Mikroudz/sulautetut-jarjestelmat/STM32F410/Src/vl53l1_platform.c

/* 
* This file is part of VL53L1 Platform 
* 
* Copyright (c) 2016, STMicroelectronics - All Rights Reserved 
* 
* License terms: BSD 3-clause "New" or "Revised" License. 
* 
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
* 3. Neither the name of the copyright holder nor the names of its contributors 
* may be used to endorse or promote products derived from this software 
* without specific prior written permission. 
* 
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
*/

#include "vl53l1_platform.h"
#include <string.h>
#include <time.h>
#include <math.h>
#include "vl53l1_error_codes.h"

#include "i2c.h"

#define I2C_TIME_OUT_BASE   10
#define I2C_TIME_OUT_BYTE   1

/* when not customized by application define dummy one */
#ifndef VL53L1_GetI2cBus
/** This macro can be overloaded by user to enforce i2c sharing in RTOS context
 */
#   define VL53L1_GetI2cBus(...) (void)0
#endif

#ifndef VL53L1_PutI2cBus
/** This macro can be overloaded by user to enforce i2c sharing in RTOS context
 */
#   define VL53L1_PutI2cBus(...) (void)0
#endif
I2C_HandleTypeDef hi2c2;


uint8_t _I2CBuffer[256];

int _I2CWrite(uint16_t Dev, uint8_t *pdata, uint32_t count) {
    int status;
    int i2c_time_out = I2C_TIME_OUT_BASE + count * I2C_TIME_OUT_BYTE;

    status = HAL_I2C_Master_Transmit(&hi2c2, Dev, pdata, count, i2c_time_out);
    if (status) {
        //VL6180x_ErrLog("I2C error 0x%x %d len", dev->I2cAddr, len);
        //XNUCLEO6180XA1_I2C1_Init(&hi2c2);
    }
    return status;
}

// Alustava DMA-funktio, ei vielä käytössä
int _I2CWrite_DMA(uint16_t Dev, uint8_t *pdata, uint32_t count) {
    int status;

    status = HAL_I2C_Master_Transmit_DMA(&hi2c2, Dev, pdata, count);
    if (status) {
        //VL6180x_ErrLog("I2C error 0x%x %d len", dev->I2cAddr, len);
        //XNUCLEO6180XA1_I2C1_Init(&hi2c2);
    }
    return status;
}

int _I2CRead(uint16_t Dev, uint8_t *pdata, uint32_t count) {
    int status;
    int i2c_time_out = I2C_TIME_OUT_BASE+ count* I2C_TIME_OUT_BYTE;

    status = HAL_I2C_Master_Receive(&hi2c2, Dev | 1, pdata, count, i2c_time_out);
    if (status) {
        //VL6180x_ErrLog("I2C error 0x%x %d len", dev->I2cAddr, len);
        //XNUCLEO6180XA1_I2C1_Init(&hi2c2);
    }
    return status;
}

// Alustava DMA-funktio, ei vielä käytössä
int _I2CRead_DMA(uint16_t Dev, uint8_t *pdata, uint32_t count){
    int status;

    status = HAL_I2C_Master_Receive_DMA(&hi2c2, Dev | 1, pdata, count);
    if (status) {
        //VL6180x_ErrLog("I2C error 0x%x %d len", dev->I2cAddr, len);
        //XNUCLEO6180XA1_I2C1_Init(&hi2c2);
    }
    return status;
}

int8_t VL53L1_WriteMulti( uint16_t Dev, uint16_t index, uint8_t *pdata, uint32_t count) {
	int status_int;
    VL53L1_Error Status = VL53L1_ERROR_NONE;
    if (count > sizeof(_I2CBuffer) - 1) {
        return VL53L1_ERROR_INVALID_PARAMS;
    }
    _I2CBuffer[0] = index>>8;
    _I2CBuffer[1] = index&0xFF;
    memcpy(&_I2CBuffer[2], pdata, count);
    VL53L1_GetI2cBus();
    status_int = _I2CWrite(Dev, _I2CBuffer, count + 2);
    if (status_int != 0) {
        Status = VL53L1_ERROR_CONTROL_INTERFACE;
    }
    VL53L1_PutI2cBus();
    return Status;
}

VL53L1_Error VL53L1_ReadMulti(uint16_t Dev, uint16_t index, uint8_t *pdata, uint32_t count) {
    VL53L1_Error Status = VL53L1_ERROR_NONE;
    int32_t status_int;

    _I2CBuffer[0] = index>>8;
    _I2CBuffer[1] = index&0xFF;
    VL53L1_GetI2cBus();
    status_int = _I2CWrite(Dev, _I2CBuffer, 2);
    if (status_int != 0) {
        Status = VL53L1_ERROR_CONTROL_INTERFACE;
        goto done;
    }
    status_int = _I2CRead(Dev, pdata, count);
    if (status_int != 0) {
        Status = VL53L1_ERROR_CONTROL_INTERFACE;
    }
done:
    VL53L1_PutI2cBus();
    return Status;
}

VL53L1_Error VL53L1_WrByte(uint16_t Dev, uint16_t index, uint8_t data) {
    VL53L1_Error Status = VL53L1_ERROR_NONE;
    int32_t status_int;

    _I2CBuffer[0] = index>>8;
    _I2CBuffer[1] = index&0xFF;
    _I2CBuffer[2] = data;

    VL53L1_GetI2cBus();
    status_int = _I2CWrite(Dev, _I2CBuffer, 3);
    if (status_int != 0) {
        Status = VL53L1_ERROR_CONTROL_INTERFACE;
    }
    VL53L1_PutI2cBus();
    return Status;
}

VL53L1_Error VL53L1_WrWord(uint16_t Dev, uint16_t index, uint16_t data) {
    VL53L1_Error Status = VL53L1_ERROR_NONE;
    int32_t status_int;

    _I2CBuffer[0] = index>>8;
    _I2CBuffer[1] = index&0xFF;
    _I2CBuffer[2] = data >> 8;
    _I2CBuffer[3] = data & 0x00FF;

    VL53L1_GetI2cBus();
    status_int = _I2CWrite(Dev, _I2CBuffer, 4);
    if (status_int != 0) {
        Status = VL53L1_ERROR_CONTROL_INTERFACE;
    }
    VL53L1_PutI2cBus();
    return Status;
}

VL53L1_Error VL53L1_WrDWord(uint16_t Dev, uint16_t index, uint32_t data) {
    VL53L1_Error Status = VL53L1_ERROR_NONE;
    int32_t status_int;
    _I2CBuffer[0] = index>>8;
    _I2CBuffer[1] = index&0xFF;
    _I2CBuffer[2] = (data >> 24) & 0xFF;
    _I2CBuffer[3] = (data >> 16) & 0xFF;
    _I2CBuffer[4] = (data >> 8)  & 0xFF;
    _I2CBuffer[5] = (data >> 0 ) & 0xFF;
    VL53L1_GetI2cBus();
    status_int = _I2CWrite(Dev, _I2CBuffer, 6);
    if (status_int != 0) {
        Status = VL53L1_ERROR_CONTROL_INTERFACE;
    }
    VL53L1_PutI2cBus();
    return Status;
}

VL53L1_Error VL53L1_UpdateByte(uint16_t Dev, uint16_t index, uint8_t AndData, uint8_t OrData) {
    VL53L1_Error Status = VL53L1_ERROR_NONE;
    uint8_t data;

    Status = VL53L1_RdByte(Dev, index, &data);
    if (Status) {
        goto done;
    }
    data = (data & AndData) | OrData;
    Status = VL53L1_WrByte(Dev, index, data);
done:
    return Status;
}

VL53L1_Error VL53L1_RdByte(uint16_t Dev, uint16_t index, uint8_t *data) {
    VL53L1_Error Status = VL53L1_ERROR_NONE;
    int32_t status_int;

	_I2CBuffer[0] = index>>8;
	_I2CBuffer[1] = index&0xFF;
    VL53L1_GetI2cBus();
    status_int = _I2CWrite(Dev, _I2CBuffer, 2);
    if( status_int ){
        Status = VL53L1_ERROR_CONTROL_INTERFACE;
        goto done;
    }
    status_int = _I2CRead(Dev, data, 1);
    if (status_int != 0) {
        Status = VL53L1_ERROR_CONTROL_INTERFACE;
    }
done:
    VL53L1_PutI2cBus();
    return status_int;
}

VL53L1_Error VL53L1_RdWord(uint16_t Dev, uint16_t index, uint16_t *data) {
    VL53L1_Error Status = VL53L1_ERROR_NONE;
    int32_t status_int;

    _I2CBuffer[0] = index>>8;
	_I2CBuffer[1] = index&0xFF;
    VL53L1_GetI2cBus();
    status_int = _I2CWrite(Dev, _I2CBuffer, 2);

    if( status_int ){
        Status = VL53L1_ERROR_CONTROL_INTERFACE;
        goto done;
    }
    status_int = _I2CRead(Dev, _I2CBuffer, 2);
    if (status_int != 0) {
        Status = VL53L1_ERROR_CONTROL_INTERFACE;
        goto done;
    }

    *data = ((uint16_t)_I2CBuffer[0]<<8) + (uint16_t)_I2CBuffer[1];
done:
    VL53L1_PutI2cBus();
    return Status;
}

VL53L1_Error VL53L1_RdWord_DMA(uint16_t Dev, uint16_t index, uint16_t *data) {
    VL53L1_Error Status = VL53L1_ERROR_NONE;
    int32_t status_int;

    _I2CBuffer[0] = index>>8;
	_I2CBuffer[1] = index&0xFF;
    VL53L1_GetI2cBus();
    status_int = _I2CWrite_DMA(Dev, _I2CBuffer, 2);

    if( status_int ){
        Status = VL53L1_ERROR_CONTROL_INTERFACE;
        goto done;
    }
    status_int = _I2CRead_DMA(Dev, _I2CBuffer, 2);
    if (status_int != 0) {
        Status = VL53L1_ERROR_CONTROL_INTERFACE;
        goto done;
    }

    *data = ((uint16_t)_I2CBuffer[0]<<8) + (uint16_t)_I2CBuffer[1];
done:
    VL53L1_PutI2cBus();
    return Status;
}

VL53L1_Error VL53L1_RdDWord(uint16_t Dev, uint16_t index, uint32_t *data) {
    VL53L1_Error Status = VL53L1_ERROR_NONE;
    int32_t status_int;

    _I2CBuffer[0] = index>>8;
	_I2CBuffer[1] = index&0xFF;
    VL53L1_GetI2cBus();
    status_int = _I2CWrite(Dev, _I2CBuffer, 2);
    if (status_int != 0) {
        Status = VL53L1_ERROR_CONTROL_INTERFACE;
        goto done;
    }
    status_int = _I2CRead(Dev, _I2CBuffer, 4);
    if (status_int != 0) {
        Status = VL53L1_ERROR_CONTROL_INTERFACE;
        goto done;
    }

    *data = ((uint32_t)_I2CBuffer[0]<<24) + ((uint32_t)_I2CBuffer[1]<<16) + ((uint32_t)_I2CBuffer[2]<<8) + (uint32_t)_I2CBuffer[3];

done:
    VL53L1_PutI2cBus();
    return Status;
}

VL53L1_Error VL53L1_WaitMs(uint16_t dev, int32_t wait_ms){
	(void)dev;
	HAL_Delay(wait_ms);
    return VL53L1_ERROR_NONE;
}

VL53L1_Error VL53L1_WaitUs(uint16_t dev, int32_t wait_us){
	(void)dev;
	HAL_Delay(wait_us/1000);
    return VL53L1_ERROR_NONE;
}

VL53L1_Error VL53L1_GetTickCount(
	uint32_t *ptick_count_ms)
{

    /* Returns current tick count in [ms] */

	VL53L1_Error status  = VL53L1_ERROR_NONE;

	//*ptick_count_ms = timeGetTime();
	*ptick_count_ms = 0;

#ifdef VL53L1_LOG_ENABLE
	trace_print(
		VL53L1_TRACE_LEVEL_DEBUG,
		"VL53L1_GetTickCount() = %5u ms;\n",
	*ptick_count_ms);
#endif

	return status;
}

VL53L1_Error VL53L1_WaitValueMaskEx(
	uint16_t 			dev,
	uint32_t      timeout_ms,
	uint16_t      index,
	uint8_t       value,
	uint8_t       mask,
	uint32_t      poll_delay_ms)
{

	/*
	 * Platform implementation of WaitValueMaskEx V2WReg script command
	 *
	 * WaitValueMaskEx(
	 *          duration_ms,
	 *          index,
	 *          value,
	 *          mask,
	 *          poll_delay_ms);
	 */

	VL53L1_Error status         = VL53L1_ERROR_NONE;
	uint32_t     start_time_ms = 0;
	uint32_t     current_time_ms = 0;
	uint32_t     polling_time_ms = 0;
	uint8_t      byte_value      = 0;
	uint8_t      found           = 0;
#ifdef VL53L1_LOG_ENABLE
	uint8_t      trace_functions = VL53L1_TRACE_FUNCTION_NONE;
#endif

//	char   register_name[VL53L1_MAX_STRING_LENGTH];

    /* look up register name */
#ifdef PAL_EXTENDED
	VL53L1_get_register_name(
			index,
			register_name);
#else
//	VL53L1_COPYSTRING(register_name, "");
#endif

	/* Output to I2C logger for FMT/DFT  */

    /*trace_i2c("WaitValueMaskEx(%5d, 0x%04X, 0x%02X, 0x%02X, %5d);\n",
    		     timeout_ms, index, value, mask, poll_delay_ms); */
   // trace_i2c("WaitValueMaskEx(%5d, %s, 0x%02X, 0x%02X, %5d);\n",
    //		     timeout_ms, register_name, value, mask, poll_delay_ms);

	/* calculate time limit in absolute time */

	 VL53L1_GetTickCount(&start_time_ms);

	/* remember current trace functions and temporarily disable
	 * function logging
	 */

#ifdef VL53L1_LOG_ENABLE
	trace_functions = VL53L1_get_trace_functions();
	VL53L1_set_trace_functions(VL53L1_TRACE_FUNCTION_NONE);
#endif

	/* wait until value is found, timeout reached on error occurred */

	while ((status == VL53L1_ERROR_NONE) &&
		   (polling_time_ms < timeout_ms) &&
		   (found == 0)) {

		if (status == VL53L1_ERROR_NONE)
			status = VL53L1_RdByte(
							dev,
							index,
							&byte_value);

		if ((byte_value & mask) == value)
			found = 1;

		if (status == VL53L1_ERROR_NONE  &&
			found == 0 &&
			poll_delay_ms > 0)
			status = VL53L1_WaitMs(
					dev,
					poll_delay_ms);

		/* Update polling time (Compare difference rather than absolute to
		negate 32bit wrap around issue) */
		VL53L1_GetTickCount(&current_time_ms);
		polling_time_ms = current_time_ms - start_time_ms;

	}

#ifdef VL53L1_LOG_ENABLE
	/* Restore function logging */
	VL53L1_set_trace_functions(trace_functions);
#endif

	if (found == 0 && status == VL53L1_ERROR_NONE)
		status = VL53L1_ERROR_TIME_OUT;

	return status;
}
